ParmentierGil/SmartVendorPublic/Constructie/103955373_2162351193910600_3080670010882422806_n.jpg

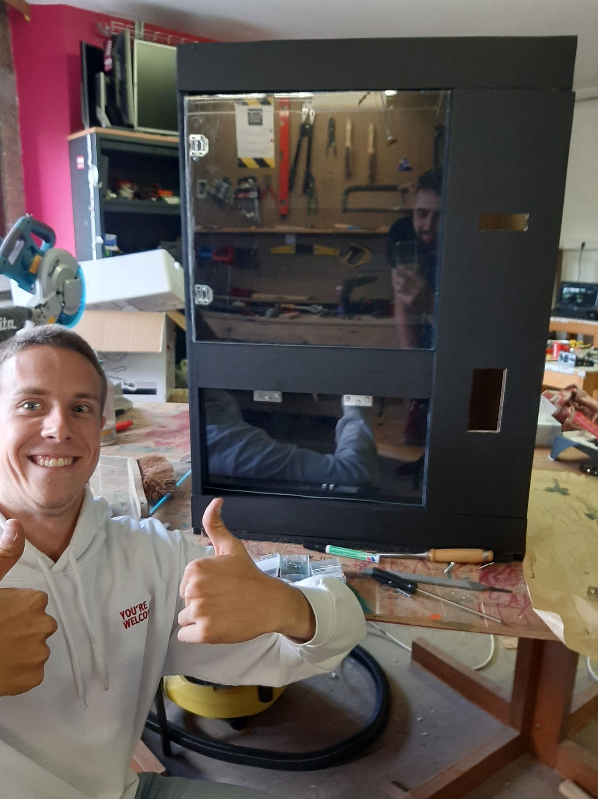
Constructie/103955373_2162351193910600_3080670010882422806_n.jpg
